peterbalch/ECG_PPG/FakeInput.h

//-----------------------------------------------------------------------------
// Fake input for ECG and PPG
//-----------------------------------------------------------------------------

#ifdef bFakeInput
//-----------------------------------------------------------------------------
const uint8_t data[] PROGMEM = {
  215, 232, 219, 187, 126, 94, 78, 85, 100, 105, 103, 101, 100, 101, 100, 100, 99, 99, 100, 102, 103,
  103, 103, 102, 102, 103, 105, 106, 106, 106, 107, 109, 112, 113, 115, 117, 121, 122, 123, 123, 126, 129,
  134, 136, 137, 137, 138, 140, 143, 142, 136, 132, 129, 127, 120, 114, 107, 107, 107, 105, 100, 98, 99,
  98, 94, 93, 93, 95, 97, 97, 97, 97, 96, 95, 96, 97, 98, 97, 96, 96, 95, 95, 94, 95,
  97, 98, 97, 96, 97, 98, 100, 101, 101, 101, 102, 102, 101, 99, 98, 98, 98, 98, 96, 95, 96,
  96, 96, 96, 96, 97, 99, 100, 101, 102, 103, 104, 104, 104, 102, 101, 102, 103, 107, 108, 107, 105,
  102, 100, 96, 93, 92, 93, 93, 93, 93, 93, 92, 90, 89, 90, 91, 90, 87, 87, 87, 85, 82,
  89, 120, 153, 202, 223, 219, 190, 125, 89, 71, 80, 96, 97, 91, 88, 90, 91, 92, 92, 94, 95,
  94, 94, 96, 98, 100, 101, 103, 104, 105, 104, 104, 105, 109, 111, 112, 112, 110, 111, 115, 120, 125,
  127, 130, 133, 137, 140, 141, 142, 143, 143, 139, 137, 136, 136, 132, 126, 117, 114, 113, 112, 106, 102,
  99, 99, 98, 96, 95, 94, 96, 96, 96, 96, 96, 95, 95, 94, 93, 91, 89, 89, 92, 94, 95,
  95, 94, 95, 97, 96, 95, 94, 93, 93, 93, 92, 92, 92, 92, 92, 91, 91, 89, 88, 88, 88,
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
  static int i = 0;
  static float f = 0;

  Rate = Rate + dRate;
  if (Rate > 2)
    dRate = -0.00001*random(100);
  if (Rate < 0.8)
    dRate = +0.00001*random(100);

  f = f+Rate;
  i = (int)f % sizeof(data);

  t++;
  if (getdata(i) > 200)
    t = 0;

  return min(getdata(i)*4,1023);
}
#endif
