peterbalch/ECG_PPG/SimpleILI9341.h

/***************************************************
  Arduino TFT graphics library for the ILI9341

  Derived from the TFT_ILI9341 library which was
  derived from the Adafruit_GFX library and the
  associated driver library.

 ****************************************************/

#ifndef SimpleILI9341_h
#define SimpleILI9341_h

#include <SPI.h>

extern int Cursorx,Cursory;
extern uint16_t tft_width, tft_height; // Display w/h
extern bool execDrawChar;
extern uint8_t pen_width; // if pen_width > 1 then draws with a disc of radius pen_width
extern bool ILI9341fast; // true is faster but can interfere with other devices on SPI bus; false shares the SPI bus better
extern uint8_t letter_gap;

// ILI9341 rotation values
#define ILI9341_MADCTL_MY  0x80
#define ILI9341_MADCTL_MX  0x40
#define ILI9341_MADCTL_MV  0x20
#define ILI9341_MADCTL_ML  0x10
#define ILI9341_MADCTL_RGB 0x00
#define ILI9341_MADCTL_BGR 0x08
#define ILI9341_MADCTL_MH  0x04

#define ILI9341_Rotation0  (ILI9341_MADCTL_MX | ILI9341_MADCTL_BGR)
#define ILI9341_Rotation1  (ILI9341_MADCTL_MV | ILI9341_MADCTL_BGR)
#define ILI9341_Rotation2  (ILI9341_MADCTL_MY | ILI9341_MADCTL_BGR)
#define ILI9341_Rotation3  (ILI9341_MADCTL_MX | ILI9341_MADCTL_MY | ILI9341_MADCTL_MV | ILI9341_MADCTL_BGR)

void ILI9341Begin(uint8_t CS = 10, uint8_t CD = 8, uint8_t RST = 7, uint16_t w = 320, uint16_t h = 240, uint8_t Rotation = ILI9341_Rotation1);
void ILI9341SetCursor(uint16_t x, uint16_t y);
void ClearDisplay(uint16_t color);
void DrawLine(uint16_t x1, uint16_t y1, uint16_t x2, uint16_t y2, uint16_t color);
void DrawPixel(uint16_t x, uint16_t y, uint16_t color);
void DrawHLine(uint16_t x, uint16_t y, uint16_t w, uint16_t color);
void DrawVLine(uint16_t x, uint16_t y, uint16_t h, uint16_t color);
void DrawBox(uint16_t x, uint16_t y, uint16_t w, uint16_t h, uint16_t color);
void DrawFrame(uint16_t x, uint16_t y, uint16_t w, uint16_t h, uint16_t color);
void DrawRoundRect(uint16_t x, uint16_t y, uint16_t w, uint16_t h, uint16_t rad, uint16_t color);
void DrawCircle(uint16_t x0, uint16_t y0, uint16_t rad, uint16_t color);
void DrawDisc(uint16_t x0, uint16_t y0, uint16_t rad, uint16_t color);
void DrawFilledEllipse(int x0, int y0, int rx, int ry, uint16_t color);
void DrawEllipse(int x0, int y0, int rx, int ry, uint16_t color);
void DrawTriangle(uint16_t x0, uint16_t y0, uint16_t x1, uint16_t y1, uint16_t x2, uint16_t y2, uint16_t color);
void DrawChar(uint8_t c, word Font, uint16_t color);
void DrawString(char * s, word Font, uint16_t color);
void DrawStringAt(int16_t x, int16_t y, char * s, word Font, uint16_t color);
void DrawStringF(word s, byte *Font, uint16_t color); // Draw String using the F macro to put the string in flash
void DrawInt(int i, word Font, uint16_t color);
void DrawFloat(float floatNumber, int dp, word Font, uint16_t color);
void InvertDisplay(boolean i);
uint16_t rgb(uint8_t r, uint8_t g, uint8_t b);
void DrawBitmap(int16_t x, int16_t y, const unsigned short *bitmap);
void DrawBitmapMono(int16_t x, int16_t y, const uint8_t *bitmap, uint16_t color);

void BeginTouch(uint8_t CS = 2, uint8_t Rotation = 1, int xmin = 320, int ymin = 320, int xmax = 3900, int ymax = 3900);
bool GetTouch(int *x, int *y);

#include <Arduino.h>

// color definitions

#define RGB(r, g, b)  (((r & 0xF8) << 8) | ((g & 0xFC) << 3) | (b >> 3))
#define TFT_BLACK       RGB(0,   0,   0)
#define TFT_NAVY        RGB(0,   0, 128)
#define TFT_DARKGREEN   RGB(0, 128,   0)
#define TFT_DARKCYAN    RGB(0, 128, 128)
#define TFT_MAROON      RGB(128,   0,   0)
#define TFT_PURPLE      RGB(128,   0, 128)
#define TFT_OLIVE       RGB(128, 128,   0)
#define TFT_LIGHTGREY   RGB(192, 192, 192)
#define TFT_LIGHTGRAY   RGB(192, 192, 192)
#define TFT_DARKGREY    RGB(128, 128, 128)
#define TFT_DARKGRAY    RGB(128, 128, 128)
#define TFT_BLUE        RGB(0,   0, 255)
#define TFT_GREEN       RGB(0, 255,   0)
#define TFT_CYAN        RGB(0, 255, 255)
#define TFT_RED         RGB(255,   0,   0)
#define TFT_MAGENTA     RGB(255,   0, 255)
#define TFT_YELLOW      RGB(255, 255,   0)
#define TFT_WHITE       RGB(255, 255, 255)
#define TFT_ORANGE      RGB(255, 165,   0)

const byte SmallFont[] PROGMEM = {
  7, // ymax
  1, // descender
  ' ', //first char
  3, 0x00,0x00,0x00,                           // space
  1, 0xFA,                                     // !
  3, 0xC0,0x00,0xC0,                           // "
  5, 0x28,0xFE,0x28,0xFE,0x28,                 // #
  5, 0x24,0x52,0xFF,0x4A,0x24,                 // dollar
  6, 0x62,0x64,0x08,0x10,0x26,0x46,            // %
  5, 0x5C,0xA2,0x52,0x0C,0x12,                 // &
  1, 0xC0,                                     // '
  2, 0x7E,0x81,                                // (
  2, 0x81,0x7E,                                // )
  2, 0xC0,0xC0,                                // *
  5, 0x08,0x08,0x3E,0x08,0x08,                 // +
  1, 0x03,                                     // ,
  5, 0x08,0x08,0x08,0x08,0x08,                 // -
  1, 0x02,                                     // .
  3, 0x06,0x38,0xC0,                           // /
  4, 0x7C,0x82,0x82,0x7C,                      // 0
  2, 0x40,0xFE,                                // 1
  4, 0x46,0x8A,0x92,0x62,                      // 2
  4, 0x44,0x82,0x92,0x6C,                      // 3
  4, 0x18,0x68,0xFE,0x08,                      // 4
  4, 0xF4,0xA2,0xA2,0x9C,                      // 5
  4, 0x7C,0x92,0x92,0x4C,                      // 6
  4, 0x80,0x8E,0xB0,0xC0,                      // 7
  4, 0x6C,0x92,0x92,0x6C,                      // 8
  4, 0x64,0x92,0x92,0x7C,                      // 9
  1, 0x12,                                     // :
  1, 0x13,                                     // ;
  3, 0x08,0x14,0x22,                           // <
  3, 0x14,0x14,0x14,                           // =
  3, 0x22,0x14,0x08,                           // >
  4, 0x40,0x8A,0x90,0x60,                      // ?
  8, 0x3C,0x42,0x99,0xA5,0xB9,0x85,0x44,0x38,  // @
  6, 0x06,0x38,0xC8,0xC8,0x38,0x06,            // A
  6, 0xFE,0x92,0x92,0x92,0x92,0x6C,            // B
  6, 0x7C,0x82,0x82,0x82,0x82,0x44,            // C
  6, 0xFE,0x82,0x82,0x82,0x82,0x7C,            // D
  5, 0xFE,0x92,0x92,0x92,0x82,                 // E
  5, 0xFE,0x90,0x90,0x90,0x80,                 // F
  6, 0x7C,0x82,0x82,0x92,0x94,0x5E,            // G
  6, 0xFE,0x10,0x10,0x10,0x10,0xFE,            // H
  1, 0xFE,                                     // I
  4, 0x0C,0x02,0x02,0xFC,                      // J
  5, 0xFE,0x10,0x28,0x44,0x82,                 // K
  4, 0xFE,0x02,0x02,0x02,                      // L
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
  3, 0x60,0x1C,0x03,                           // backslash
  2, 0x81,0xFF,                                // ]
  3, 0x40,0x80,0x40,                           // ^
  5, 0x02,0x02,0x02,0x02,0x02,                 // _
  2, 0x80,0x40,                                // '
  4, 0x04,0x2A,0x2A,0x1E,                      // a
  4, 0xFE,0x22,0x22,0x1C,                      // b
  4, 0x1C,0x22,0x22,0x14,                      // c
  4, 0x1C,0x22,0x22,0xFE,                      // d
  4, 0x1C,0x2A,0x2A,0x18,                      // e
  2, 0x7E,0x90,                                // f
  4, 0x19,0x25,0x25,0x3E,                      // g
  4, 0xFE,0x10,0x20,0x1E,                      // h
  1, 0xBE,                                     // i
  2, 0x01,0xBF,                                // j
  4, 0xFE,0x18,0x24,0x02,                      // k
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
  4, 0xF4,0xA2,0xA2,0x9C,                      // 5
  4, 0x7C,0x92,0x92,0x4C,                      // 6
  4, 0x80,0x8E,0xB0,0xC0,                      // 7
  4, 0x6C,0x92,0x92,0x6C,                      // 8
  4, 0x64,0x92,0x92,0x7C,                      // 9
  0}; // end

#endif
